henrikenblom/SIDPod/src/buddy/Buddy.h

//
// Created by Henrik Enblom on 2025-04-21.
//

#ifndef BLUETOOTHDEVICELIST_H
#define BLUETOOTHDEVICELIST_H
#include <cstdint>
#include <cstring>
#include <vector>

#include "delays.h"
#include "../platform_config.h"

#if USE_BUDDY

#define SCRIBBLE_TIMEOUT_MS                 500
#define BUDDY_ENABLE_PIN                    7
#define BUDDY_BT_CONNECTED_PIN              15
#define UART_READABLE_TIMEOUT_MS            100
#define MAX_CONNECTION_ATTEMPTS             3
#define LAST_BT_DEVICE_FILE                 "last_bt.txt"
#define BLINK_INTERVAL_VBL           10

enum RequestType {
    RT_NONE = 0,
    RT_BT_LIST = 1,
    RT_BT_SELECT = 2,
    RT_BT_DISCONNECT = 3,
    RT_G_FORCE_ROTATE = 4,
    RT_G_FORCE_VERTICAL = 5,
    RT_G_FORCE_HORIZONTAL = 6,
    RT_G_SET_AUTO = 7,
    RT_BT_GET_CONNECTED = 8,
    RT_SCRIBBLE = 9,
};

enum NotificationType {
    NT_NONE = 0,
    NT_GESTURE = 1,
    NT_BT_CONNECTED = 2,
    NT_BT_DISCONNECTED = 3,
    NT_BT_DEVICE_LIST_CHANGED = 4,
    NT_BT_CONNECTING = 5,
    NT_SCRIBBLE_INPUT = 6,
    NT_CHARACTER_DETECTED = 7,
    NT_BACKSPACE_DETECTED = 8,
    NT_SPACE_DETECTED = 9,
};

enum Gesture {
    G_NONE = 0,
    G_HORIZONTAL = 1,
    G_VERTICAL = 2,
    G_ROTATE = 3,
    G_TAP = 4,
    G_DOUBLE_TAP = 5,
    G_NORTH = 6,
    G_EAST = 7,
    G_WEST = 8,
    G_SOUTH = 9,
};

struct Request {
    RequestType type;
    char data[32];
};

struct BluetoothDeviceListEntry {
    char name[32];
    bool selected;
    bool connected;
};

__scratch_y("scribble") inline uint8_t scribbleBuffer[98]{};

class Buddy {
public:
    enum State {
        READY,
        REFRESHING,
        AWAITING_SELECTION,
        CONNECTING,
        CONNECTED,
        DISCONNECTED,
        AWAITING_STATE_CHANGE,
        AWAITING_DISCONNECT_CONFIRMATION,
    };

    ~Buddy() {
        devices.clear();
        window.clear();
    }

    void init();

    void addDevice(const char *name, bool selected = false);

    std::vector<BluetoothDeviceListEntry> *getWindow();

    void selectNext();

    void selectPrevious();

    void refreshDeviceList();

    [[nodiscard]] State getState() const {
        return state;
    }

    void connectSelected();

    void setDisconnected();

    void setConnecting();

    void setConnected();

    void askToDisconnect();

    void forceRotationControl();

    void forceVerticalControl();

    void enableGestureDetection();

    void disconnect();

    void enableScribbleMode();

    [[nodiscard]] RequestType getLastRequest() const;

    void scribbleBufferUpdated() {
        lastScribbleUpdate = millis();
    }

    [[nodiscard]] bool scribbleDataIsFresh() const {
        const bool isFresh = millis() < lastScribbleUpdate + SCRIBBLE_TIMEOUT_MS;
        if (!isFresh) {
            memset(scribbleBuffer, 0, 98);
        }
        return isFresh;
    }

    [[nodiscard]] const char *getConnectedDeviceName() const {
        return lastConnectedDeviceName;
    }

    [[nodiscard]] const char *getSelectedDeviceName() const {
        return selectedDeviceName;
    }

    static Buddy *getInstance();

protected:
    std::vector<BluetoothDeviceListEntry> devices;
    std::vector<BluetoothDeviceListEntry> window;
    uint8_t windowPosition = 0;
    uint8_t selectedPosition = 0;
    uint8_t windowSize = LIST_WINDOW_SIZE;
    uint8_t connectionAttempts = 0;
    RequestType lastRequest = RT_NONE;
    const char *selectedDeviceName = nullptr;
    char lastConnectedDeviceName[32]{};
    uint8_t lastConnectedAddr[6]{};
    uint32_t lastScribbleUpdate = 0;
    State state = READY;

    Buddy() = default;

    [[nodiscard]] size_t getSize() const;

    void updateWindow();

    void slideDown();

    void slideUp();

    void resetAccessors();

    static bool awaitUartReadable();

    static bool readBTDeviceName(char *buffer);

    void requestAndSetConnectedBTDeviceName();

    static void requestBTList();

    bool selectBTDevice(const char *deviceName);

    bool loadLastConnectedBTDevice();

    void saveConnectedBTDevice();

    bool reconnectSavedBTDevice();
};

#endif // USE_BUDDY

#endif //BLUETOOTHDEVICELIST_H
