henrikenblom/SIDPod/src/io/hw_config.c

/* hw_config.c
Copyright 2021 Carl John Kugler III

Licensed under the Apache License, Version 2.0 (the License); you may not use
this file except in compliance with the License. You may obtain a copy of the
License at

   http://www.apache.org/licenses/LICENSE-2.0
Unless required by applicable law or agreed to in writing, software distributed
under the License is distributed on an AS IS BASIS, WITHOUT WARRANTIES OR
CONDITIONS OF ANY KIND, either express or implied. See the License for the
specific language governing permissions and limitations under the License.
*/

/*
This file should be tailored to match the hardware design.

See
https://github.com/carlk3/no-OS-FatFS-SD-SDIO-SPI-RPi-Pico/tree/main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
*/

#include "hw_config.h"

#ifdef USE_SDCARD

/* SDIO Interface */
static sd_sdio_if_t sdio_if = {
    /*
    Pins CLK_gpio, D1_gpio, D2_gpio, and D3_gpio are at offsets from pin D0_gpio.
    The offsets are determined by sd_driver\SDIO\rp2040_sdio.pio.
        CLK_gpio = (D0_gpio + SDIO_CLK_PIN_D0_OFFSET) % 32;
        As of this writing, SDIO_CLK_PIN_D0_OFFSET is 30,
            which is -2 in mod32 arithmetic, so:
        CLK_gpio = D0_gpio -2. = 16
        D1_gpio = D0_gpio + 1 = 19
        D2_gpio = D0_gpio + 2 = 20
        D3_gpio = D0_gpio + 3 = 21
    */
    .CMD_gpio = 17,
    .D0_gpio = 18,
    .baud_rate = 125 * 1000 * 1000 / 6,
    .SDIO_PIO = pio0,
    .set_drive_strength = true,
    .CMD_gpio_drive_strength = GPIO_DRIVE_STRENGTH_2MA,
    .CLK_gpio_drive_strength = GPIO_DRIVE_STRENGTH_2MA,
    .D0_gpio_drive_strength = GPIO_DRIVE_STRENGTH_2MA,
    .D1_gpio_drive_strength = GPIO_DRIVE_STRENGTH_2MA,
    .D2_gpio_drive_strength = GPIO_DRIVE_STRENGTH_2MA,
    .D3_gpio_drive_strength = GPIO_DRIVE_STRENGTH_2MA,
};


/* Configuration of the SD Card socket object */
static __scratch_y("sd_card") sd_card_t sd_card = {.type = SD_IF_SDIO, .sdio_if_p = &sdio_if};

/* ********************************************************************** */

size_t sd_get_num() { return 1; }

/**
 * @brief Get a pointer to an SD card object by its number.
 *
 * @param[in] num The number of the SD card to get.
 *
 * @return A pointer to the SD card object, or @c NULL if the number is invalid.
 */
sd_card_t *sd_get_by_num(size_t num) {
    if (0 == num) {
        // The number 0 is a valid SD card number.
        // Return a pointer to the sd_card object.
        return &sd_card;
    } else {
        // The number is invalid. Return @c NULL.
        return NULL;
    }
}

#endif

/* [] END OF FILE */
