henrikenblom/SIDPod/src/UI.h

#ifndef SIDPOD_UI_H
#define SIDPOD_UI_H

#include "Catalog.h"
#include "display/include/ssd1306.h"

extern bool usbEjected;

class UI {
public:
    enum State {
        song_selector, splash, raster_bars, visualization, volume_control, sleeping, playlist_selector,
        refreshing_playlist, bluetooth_interaction
    };

    static void initUI();

    static void showSplash();

    static void initDanceFloor();

    static void startDanceFloor();

    static void updateUI();

    static void start(bool quickStart);

    static void stop();

    static void screenOn();

    static void screenOff();

    static void goToSleep();

    volatile static void startVolumeControlSession();

    static void resetVolumeControlSessionTimer();

    static void verticalMovement(int delta);

    static int64_t singleClickCallback(alarm_id_t id, void *user_data);

    volatile static void doubleClickCallback();

    static void danceFloorStop();

    static State getState();

    static void screenshotToPBM();

#if USE_BUDDY
    static void adjustVolume(bool up);

    static void showBluetoothInteraction();

    static void showBTConnecting();

    static void showBTDisconnectConfirmation();

    static void showBTProcessing(const char *text);

    static void showBTDeviceList();

    static bool allowFilterFunctionality();
#endif

private:
    static void showSongSelector();

    static void showPlaylistSelector();

    static void showVolumeControl();

    static inline void showRasterBars();

    static int64_t longPressCallback(alarm_id_t id, void *user_data);

    static int64_t endVolumeControlSessionCallback(alarm_id_t id, void *user_data);

    static void endVolumeControlSession();

    static void animateShutdown();

    volatile static void startSingleClickSession();

    volatile static void startDoubleClickSession();

    volatile static void startLongPressSession();

    volatile static void endSingleClickSession();

    static void endDoubleClickSession();

    static void endLongPressSession();

    volatile static bool pollSwitch();

    static bool pollUserControls(struct repeating_timer *t);

#if (!USE_BUDDY)

    volatile static void pollEncoder();

#endif
};

#endif //SIDPOD_UI_H
